saeedmOd/ESP-Prayer-System/Image_1.jpg

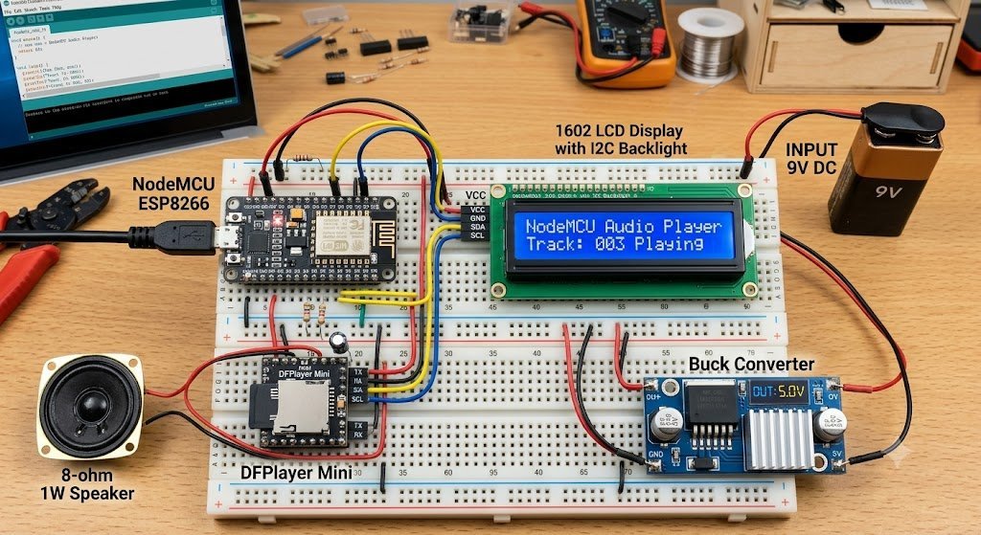
Image_1.jpg
