saeedmOd/ESP-Prayer-System/Image_2.jpg

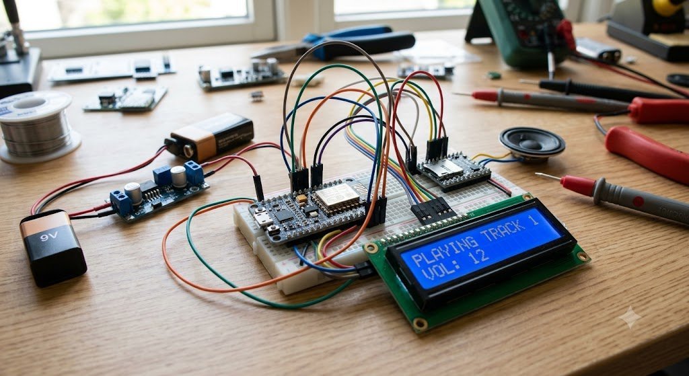
Image_2.jpg
