saeedmOd/ESP-Prayer-System/Image_4.png

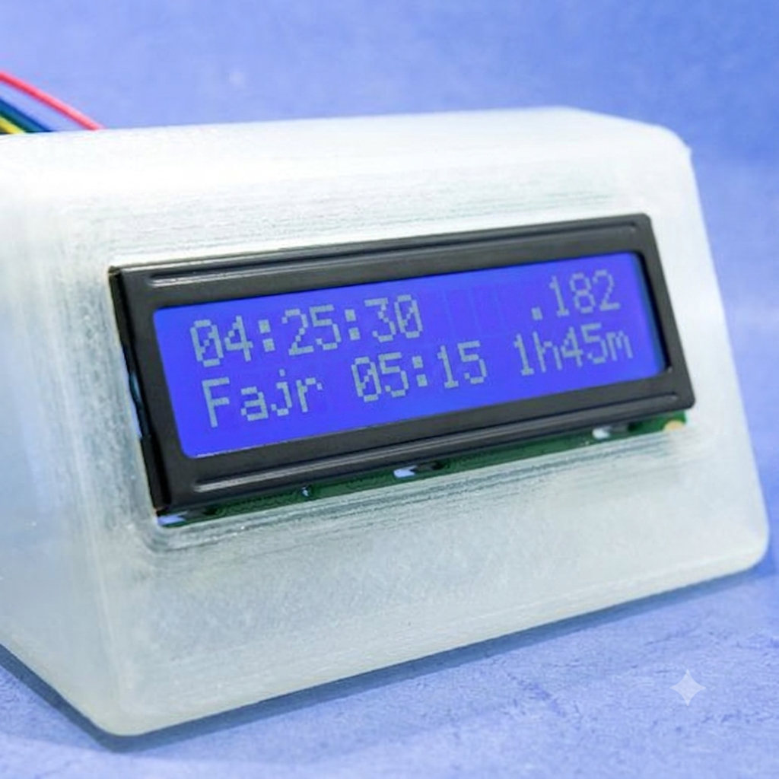
Image_4.png
