saeedmOd/ESP-Prayer-System/include/version.h

#ifndef VERSION_H
#define VERSION_H


// ================================
// Firmware Version
// ================================

#define FIRMWARE_NAME        "ESP Prayer System"

#define FIRMWARE_VERSION     "1.11.4"

#define FIRMWARE_BUILD       "2026.08.27"


// ================================
// Hardware Target
// ================================

#define HARDWARE_VERSION     "ESP8266/ESP32"


// ================================
// Developer Information
// ================================

#define AUTHOR_NAME          "Saeed"


// ================================
// Version Functions
// ================================

void print_version();


#endif
